thomasvamos/wifi_radio/wifi_radio/lockable_mpdclient.py

'''
Wrapper for a lockable MPD client
'''

from threading import Lock, Thread
from random import choice
from mpd import MPDClient

class LockableMPDClient(MPDClient):
    def __init__(self, use_unicode=False):
        super(LockableMPDClient, self).__init__()
        self.use_unicode = use_unicode
        self._lock = Lock()
    def acquire(self):
        self._lock.acquire()
    def release(self):
        self._lock.release()
    def __enter__(self):
        self.acquire()
    def __exit__(self, type, value, traceback):
        self.release()
